RobThree/WordClock/include/clock.h

#ifndef CLOCK_H
#define CLOCK_H

#include <Arduino.h>
#include <Display.h>
#include <ihandler.h>

class Clock : public IHandler
{
private:
    enum WORD
    {
        DIGIT_12,
        DIGIT_1,
        DIGIT_2,
        DIGIT_3,
        DIGIT_4,
        DIGIT_5,
        DIGIT_6,
        DIGIT_7,
        DIGIT_8,
        DIGIT_9,
        DIGIT_10,
        DIGIT_11,
        IT,
        IS,
        FIVE,
        TEN,
        TO,
        PAST,
        QUARTER,
        HALF,
        HOUR
    };

public:
    static void Handle(Time time);
    static void Initialize();

private:
    static void ShowWords(uint8_t argcount, ...);
};

#endif
