RobThree/WordClock/src/ntpclock.cpp

#include <Arduino.h>
#include <ntpclock.h>
#include <config.h>
#include <statusbar.h>
#include <display.h>

static Timezone tz;

void NTPClock::Initialize() {
    Serial.printf("Initializing NTP (server: %s, interval: %ds, timezone: %s)\n", NTP_HOST, NTP_SYNCINTERVAL, NTP_TIMEZONE);
    StatusBar::SetClockStatus(StatusBar::CLOCK_STATUS::CS_SYNCING);
    Display::Refresh();
    setServer(NTP_HOST);
    setInterval(NTP_SYNCINTERVAL);
    waitForSync();
    if (!tz.setCache(0))
        tz.setLocation(F(NTP_TIMEZONE));
    Serial.printf("NTP initialized\n");
    StatusBar::SetClockStatus(StatusBar::CLOCK_STATUS::CS_SYNCED);
    Display::Refresh();
}

long NTPClock::Now() {
    events();
    return tz.now();
}
